mrieker/pdp8l/pics/20241210_184401.jpg

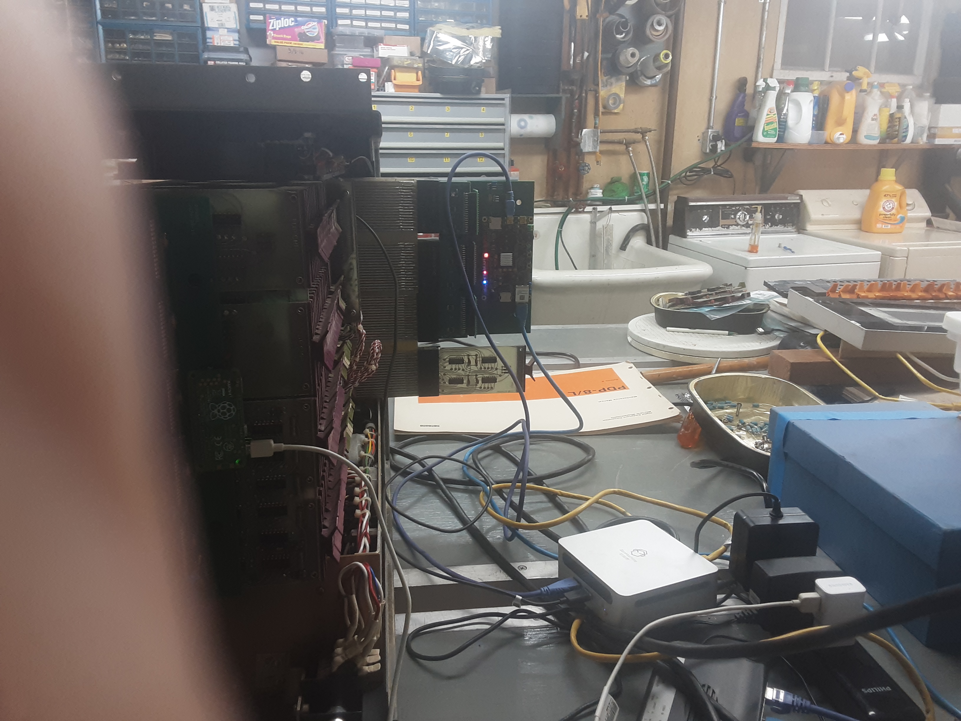
pics/20241210_184401.jpg
