mrieker/pdp8l/pics/20241210_184451.jpg

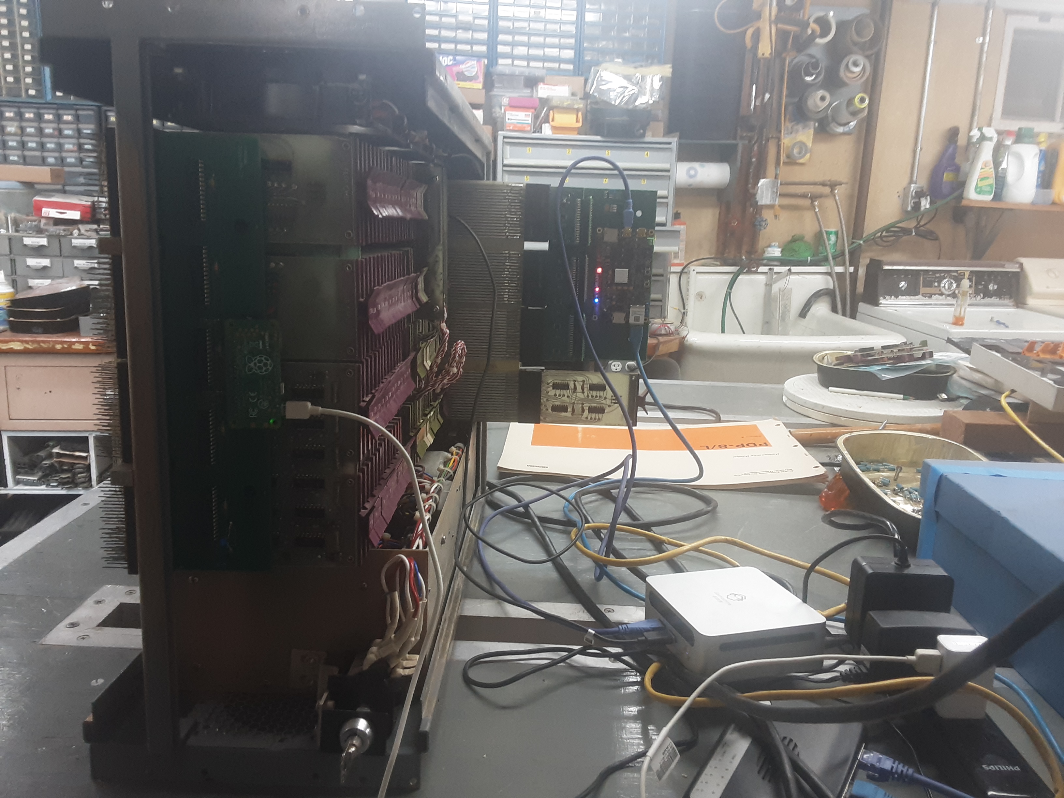
pics/20241210_184451.jpg
