mrieker/pdp8l/pics/20241210_184729.jpg

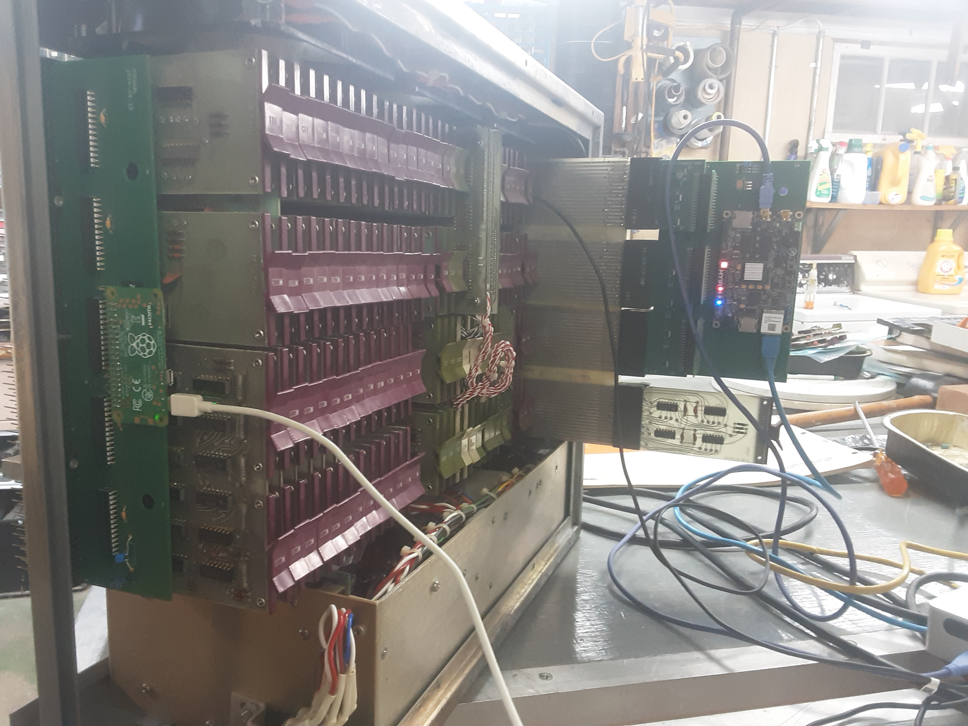
pics/20241210_184729.jpg
