mrieker/pdp8l/pics/20241225_175647.jpg

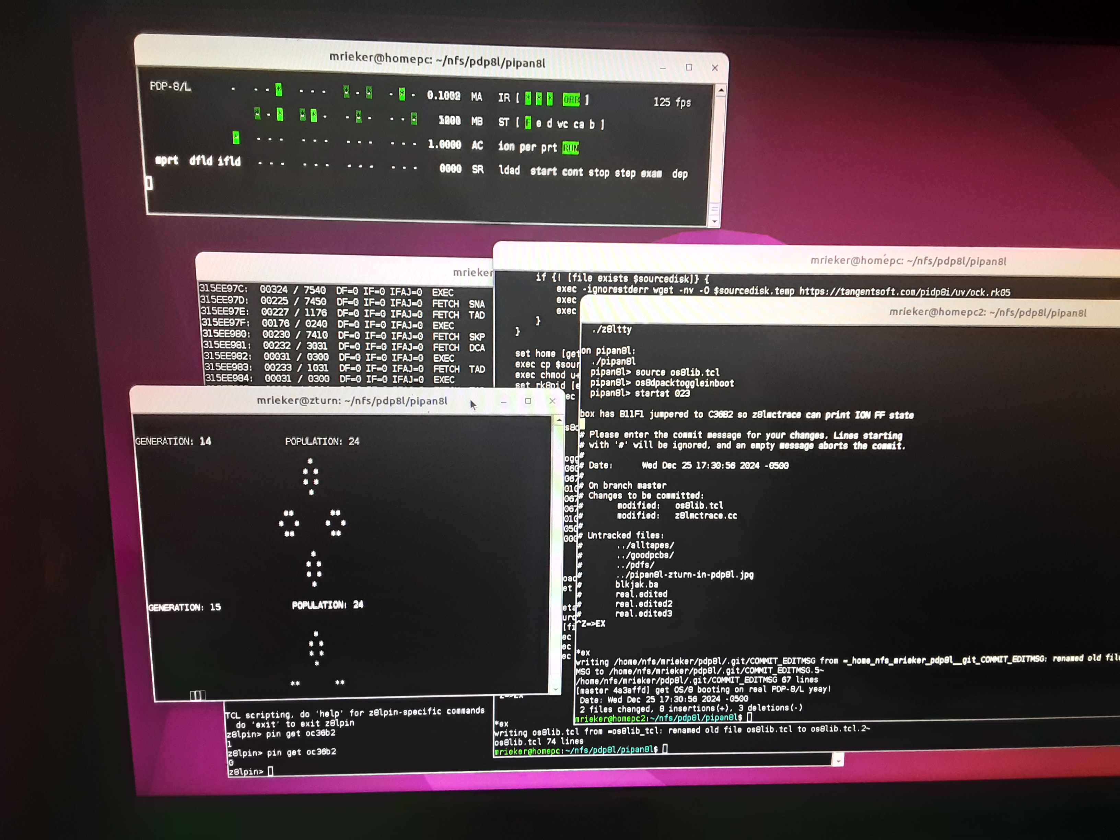
pics/20241225_175647.jpg
