mrieker/pdp8l/pics/20241225_175821.jpg

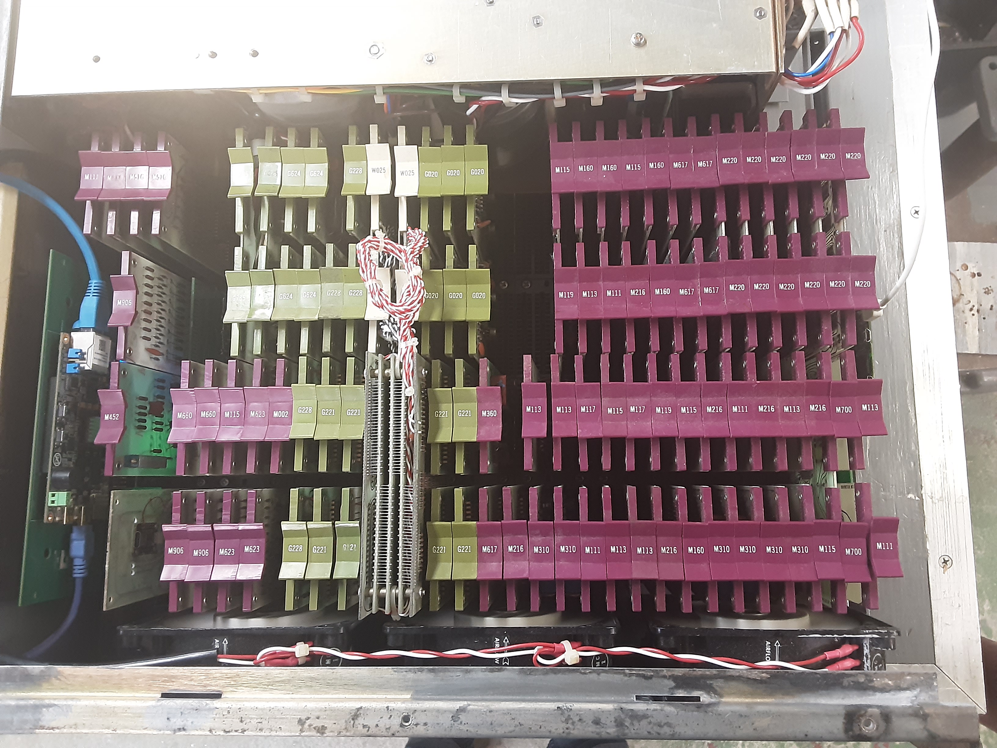
pics/20241225_175821.jpg
