mrieker/pdp8l/pics/20241225_175839.jpg

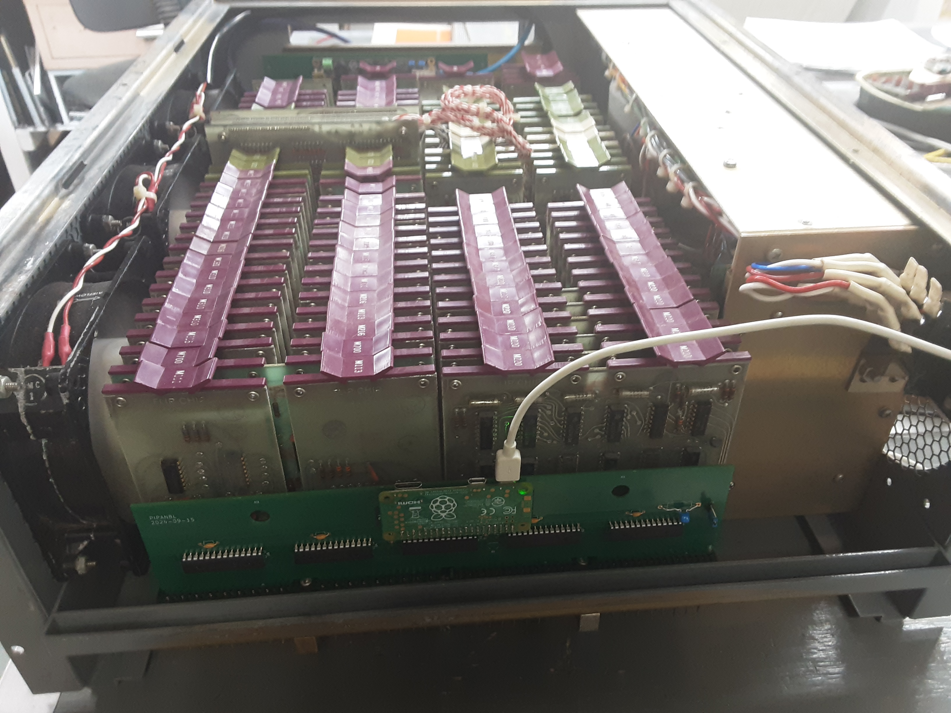
pics/20241225_175839.jpg
