mrieker/pdp8l/pics/20241225_175843.jpg

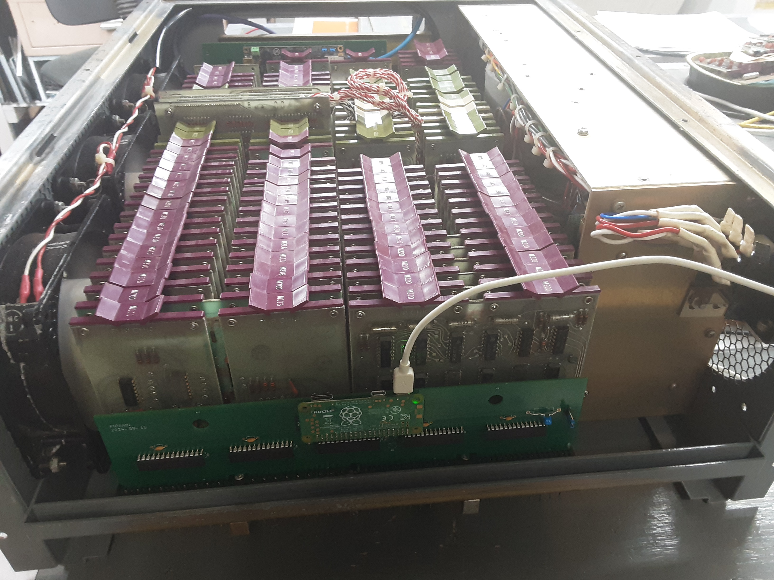
pics/20241225_175843.jpg
