mrieker/pdp8l/pics/20241225_184227.jpg

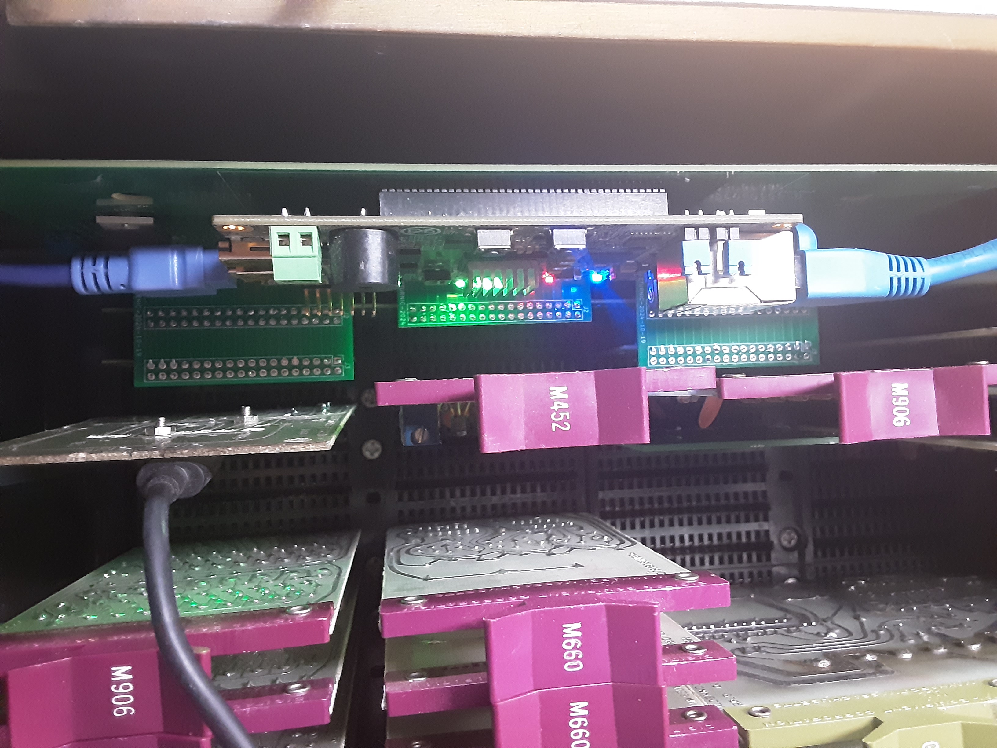
pics/20241225_184227.jpg
