mrieker/pdp8l/pics/20250225_085059.jpg

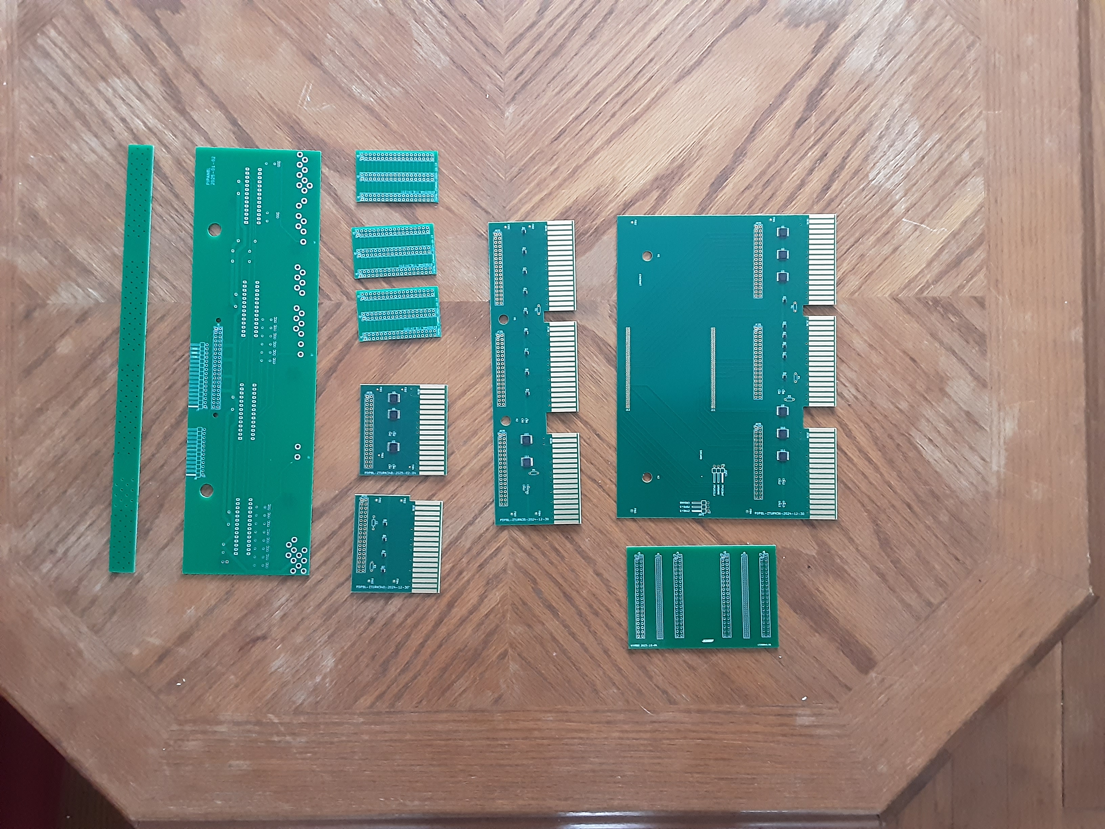
pics/20250225_085059.jpg
