mrieker/pdp8l/pics/backplane-edited.jpg

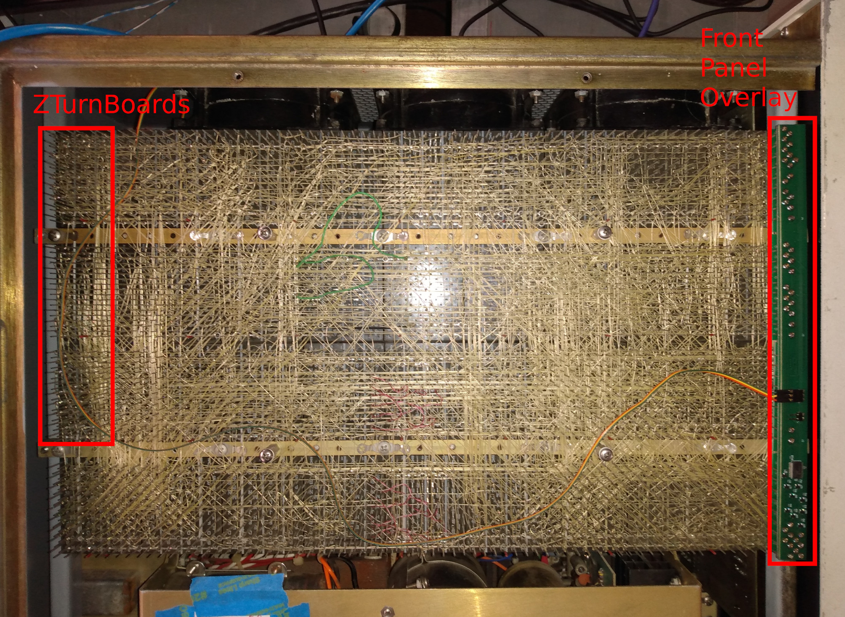
pics/backplane-edited.jpg
