mrieker/pdp8l/pipan8l/pcb3/botside.jpg

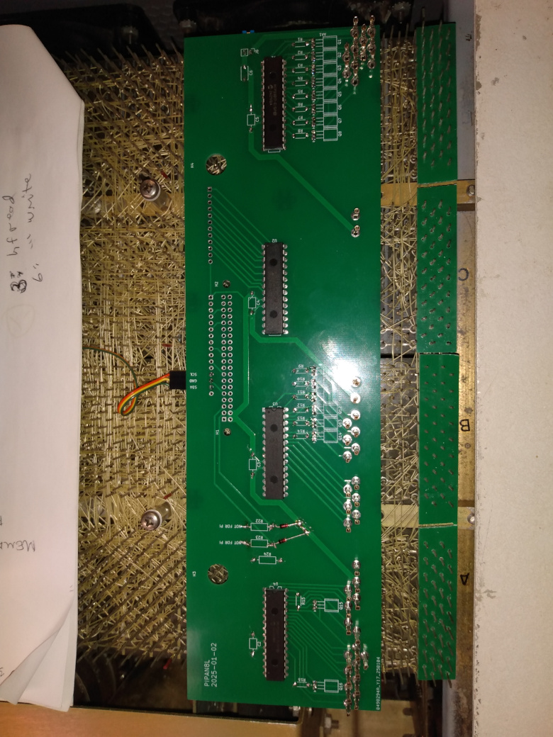
pipan8l/pcb3/botside.jpg
