mrieker/pdp8l/pipan8l/pcb3/topside.jpg

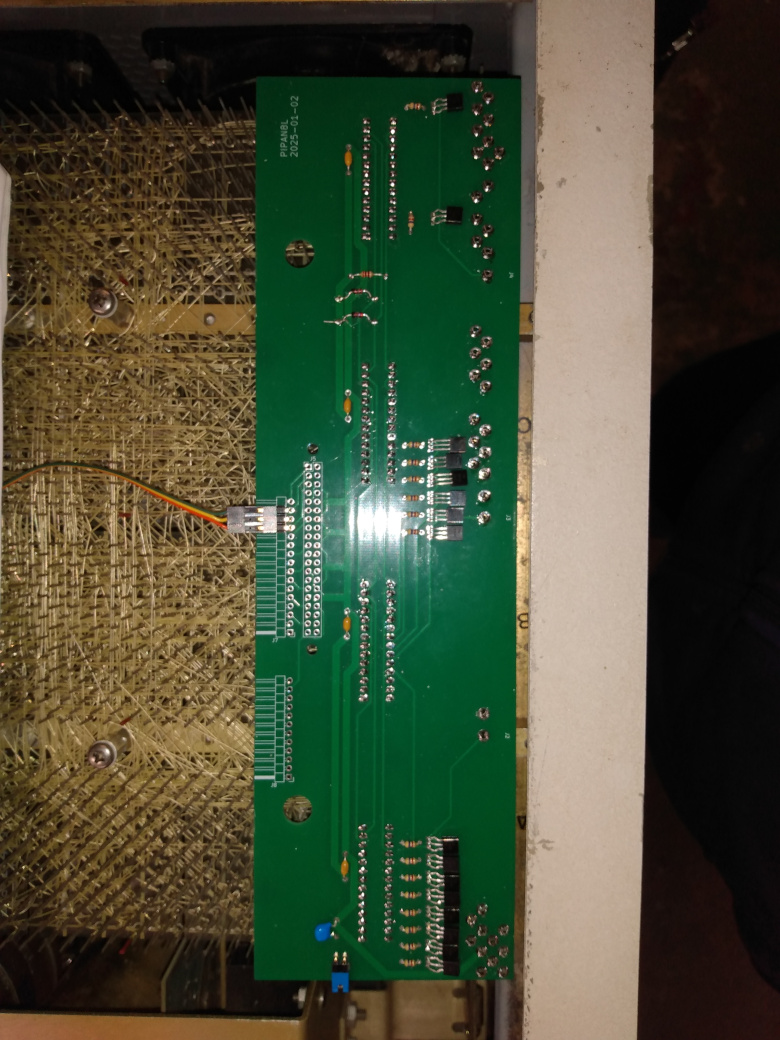
pipan8l/pcb3/topside.jpg
