mrieker/pdp8l/pipan8l/pcb4/bot-side.jpg

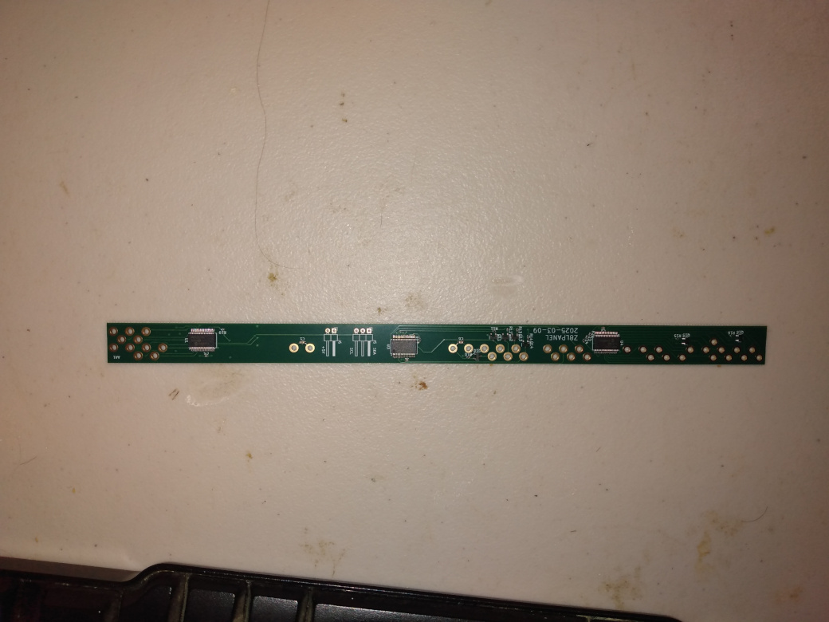
pipan8l/pcb4/bot-side.jpg
