mrieker/pdp8l/pipan8l/pcb4/plugged-in.jpg

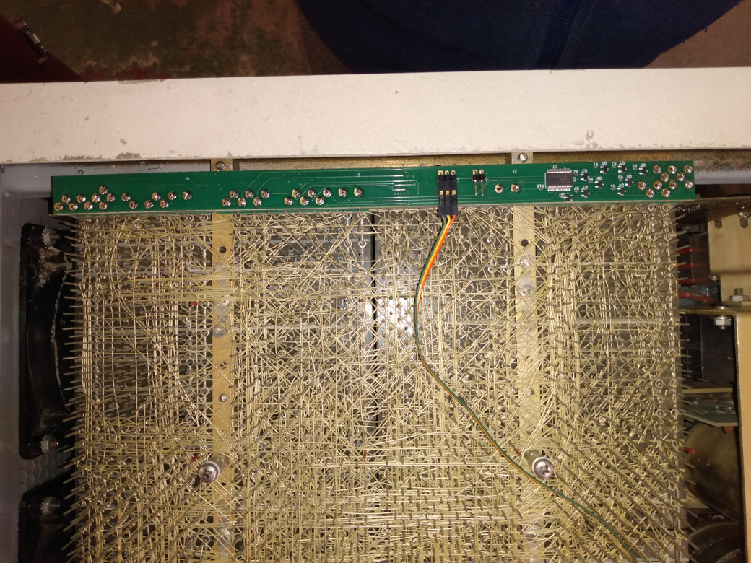
pipan8l/pcb4/plugged-in.jpg
