mrieker/pdp8l/pipan8l/pcb4/top-side.jpg

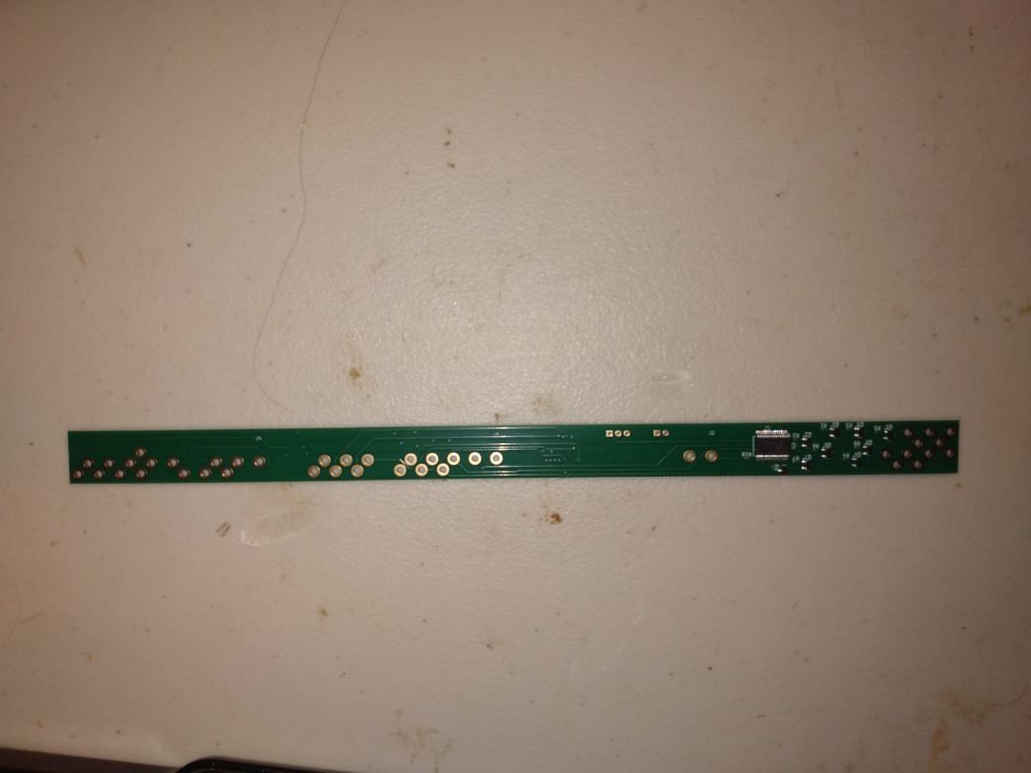
pipan8l/pcb4/top-side.jpg
