mrieker/pdp8l/ttyusbpcb/snapshot.jpg

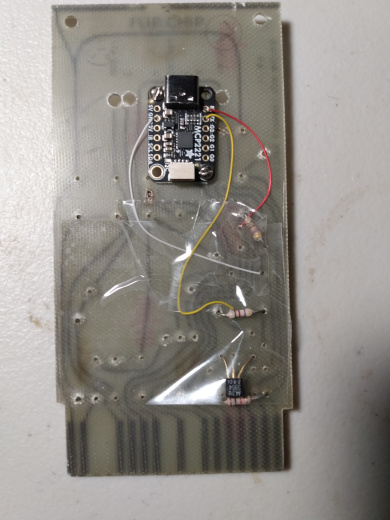
ttyusbpcb/snapshot.jpg
