mrieker/pdp8l/zturn/zturn36/zturn36snap.jpg

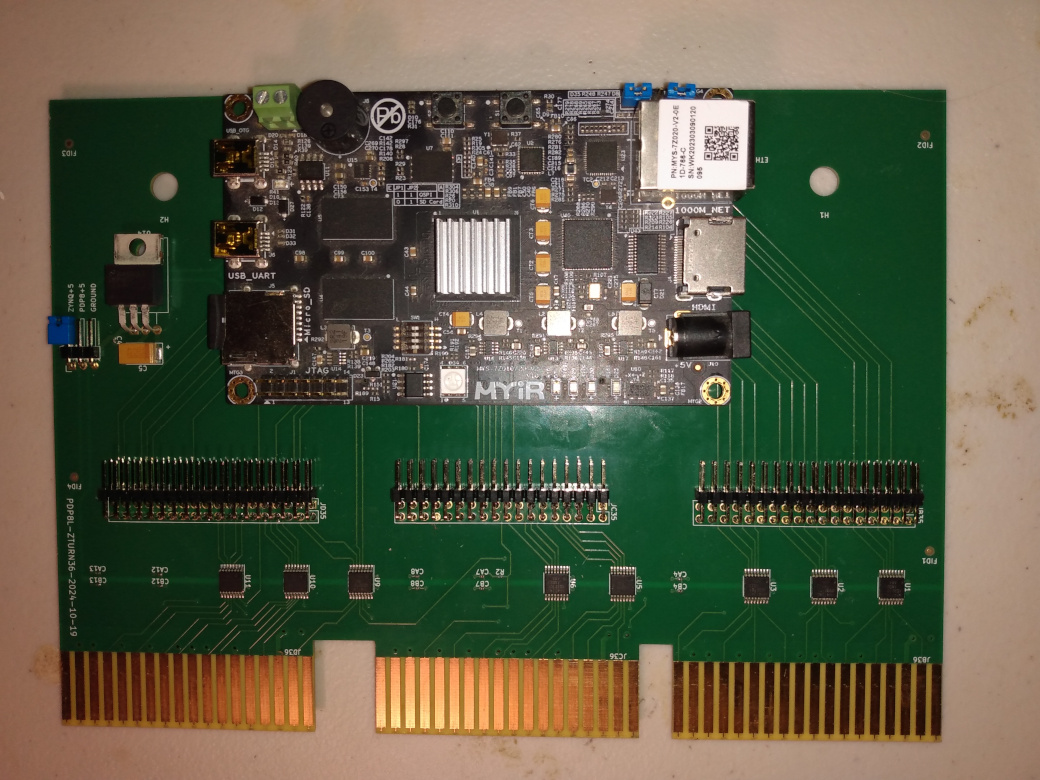
zturn/zturn36/zturn36snap.jpg
