mrieker/pdp8l/zynq/pdp8lxmem.v

//    Copyright (C) Mike Rieker, Beverly, MA USA
//    www.outerworldapps.com
//
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
//    EXPECT it to FAIL when someone's HeALTh or PROpeRTy is at RISk.
//
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
//    http://www.gnu.org/licenses/gpl-2.0.html

// PDP-8/L extended memory

// arm registers:
//  [0] = ident='XM',sizecode=1,version
//  [1] = <enable> <enlo4k> 00000000000000000000000000000 os8zap
//    enable = 0 : ignore io instructions, ie, be a dumb 4K system
//             1 : handle io instructions
//    enlo4k = 0 : PDP-8/L core stack will be used for low 4K addresses
//             1 : the low 4K of the 32K block memory will be used for low 4K addresses
//                 ...regardless of the enable bit setting
//    os8zap = 0 : nothing special
//             1 : os8 likes to do:
//                  ISZ x
//                  JMP .-1
//              ...as a delay during printing
//              zap the JMP .-1 to be:
//                  NOP ; x <= 0
//              must have enlo4k set for it to work in low 4K

//  addrlatchwid  = width to capture MA from PDP/sim
//                  TP4 of previous cycle loads MA (vol 2 p? C-7)
//  readstrobedel = delay from end of addrlatchwid to STROBE pulse
//                  time to read from RAM + make it to PDP/sim + soak thru muxes, adders, to DFF inputs
//  readstrobewid = width of STROBE pulse
//                  max 150nS or TS2 will not clear (vol 2 p? C-6)
//                  directly generates TP1 pulse
//                  TP1 delayed by 150nS is TP2 pulse
//                  TP1 delayed by 400nS is TP3 pulse
//                  TP2 loads IR during FETCH cycle
//                  TP2 loads MB during any cycle
//  writeenabdel  = delay for PDP/sim to compute writeback value in MB
//  writeenabwid  = width to write to RAM
//  writedonewid  = width of MEMDONE pulse

module pdp8lxmem (
    input CLOCK, CSTEP, RESET, BINIT,

    input armwrite,
    input[2:0] armraddr, armwaddr,
    input[31:00] armwdata,
    output[31:00] armrdata,

    input iopstart,
    input iopstop,
    input[11:00] ioopcode,
    input[11:00] cputodev,

    output reg[11:00] devtocpu,

    input freeze,

    input memstart,                 // pulse from cpu to start memory cycle (150..500nS)
    input[11:00] memaddr,
    input[11:00] memwdat,
    output reg[11:00] memrdat,
    output reg _mrdone,             // pulse to cpu saying data is available
    output reg _mwdone,             // pulse to cpu saying data has been written
    input[2:0] brkfld,              // field for dma
    output[2:0] field,              // current field being used

    input _bf_enab, _df_enab, exefet, _intack, jmpjms, ts1, ts3, tp3, _zf_enab,
    output _ea, _intinh,
    input[9:0] meminprog,
    output reg r_MA, x_MEM, hizmembus,

    input ldaddrsw,                 // load address switch
    input[2:0] ldaddfld, ldadifld,  // ifld, dfld for load address switch

    output reg[14:00] xbraddr,      // external block ram address bus
    output reg[11:00] xbrwdat,      // ... write data bus
    input[11:00] xbrrdat,           // ... read data bus
    output reg xbrenab,             // ... chip enable
    output reg xbrwena,             // ... write enable

    input  xmemblock,
    output xmemidle

    ,output reg[3:0] xmstate
    ,output reg[2:0] dfld
);

    reg ctlenab, ctllo4k, ctlwrite, intinhibeduntiljump;
    reg[2:0] lastintack;
    reg[2:0] ifld, ifldafterjump, saveddfld, savedifld;
    reg[7:0] memdelay, numcycles;
    reg[7:0] addrlatchwid, readstrobedel, readstrobewid, writeenabdel, writeenabwid, writedonewid;
    reg[9:0] exefetsr;
    reg mwhold, mwstep, mrhold, mrstep, os8zap, thisexefet;

    reg[63:00] memcycctr;

    reg[14:00] os8iszxaddr;                     // address of ISZ instruction
    reg[11:00] os8iszwdata;                     // ISZ operand value, incremented
    reg[6:0] os8iszopcad;                       // address of ISZ operand
    reg[1:0] os8step;                           // 0:looking / 1:ISZ fetch / 2:ISZ exec / 3:JMP fetch
    wire[6:0] os8jmpopcad = os8iszxaddr + 1;    // address of JMP instruction
    wire os8isourjmp = (xbraddr == { os8iszxaddr[14:07], os8jmpopcad }) &   // fetching JMP .-1 following the ISZ
                       (xbrrdat == { 5'b10101, os8iszxaddr[06:00] });

    // the _xx_enab inputs are valid in the cycle before the one they are needed in
    // ...and they go away right around the start of TS1 where they are needed
    // so we save them at the end of previous TS3 so they are valid at start of TS1 through end of TS3 that they are needed for
    reg buf_bf_enab, buf_df_enab, buf_zf_enab, lastts3;

    assign field =
                ~ buf_bf_enab ? brkfld :    // break field if cpu says so
                ~ buf_df_enab ? dfld   :    // data field if cpu says so
                ~ buf_zf_enab ? 0      :    // WC and CA cycles always use field 0
                                ifld;       // by default, use instruction field

    assign armrdata = (armraddr == 0) ? 32'h584D202E :  // [31:16] = 'XM'; [15:12] = (log2 nreg) - 1; [11:00] = version
                      (armraddr == 1) ? { ctlenab, ctllo4k, 25'b0, mrhold, mrstep, mwhold, mwstep, os8zap } :
                      (armraddr == 2) ? { _mrdone, _mwdone, field, 4'b0, dfld, ifld, ifldafterjump, saveddfld, savedifld, 4'b0, xmstate } :
                      (armraddr == 3) ? { numcycles, lastintack, buf_bf_enab, buf_df_enab, buf_zf_enab, 16'b0, os8step } :
                      (armraddr == 4) ? { writeenabdel, readstrobewid, readstrobedel, addrlatchwid } :
                      (armraddr == 5) ? { 16'b0, writedonewid, writeenabwid } :
                      (armraddr == 6) ? { memcycctr[31:00] } :
                      (armraddr == 7) ? { memcycctr[63:32] } :
                      32'hDEADBEEF;

    assign _ea = ~ (ctllo4k | (field != 0));
    assign _intinh = ~ intinhibeduntiljump;

    assign xmemidle = xmstate == 0;

    // main processing loop
    always @(posedge CLOCK) begin
        if (BINIT) begin
            if (RESET) begin
                // these get cleared on power up
                // they remain as is when start switch is pressed
                buf_bf_enab   <= 1;
                buf_df_enab   <= 1;
                buf_zf_enab   <= 1;
                ctlenab       <= 1;
                ctllo4k       <= 0;
                dfld          <= 0;
                hizmembus     <= 1;
                ifld          <= 0;
                ifldafterjump <= 0;
                lastts3       <= 0;
                mrhold        <= 0;
                mrstep        <= 0;
                mwhold        <= 0;
                mwstep        <= 0;
                os8step       <= 0;
                os8zap        <= 0;
                r_MA          <= 1;
                x_MEM         <= 1;
                xbraddr       <= 0;
                xbrwdat       <= 0;
                xbrenab       <= 0;
                xbrwena       <= 0;
                xmstate       <= 0;
                _mrdone       <= 1;
                _mwdone       <= 1;

                addrlatchwid  <=  8;                    // default extmem timing
                readstrobedel <= 35;
                readstrobewid <= 10;
                writeenabdel  <= 75;
                writeenabwid  <=  5;
                writedonewid  <= 10;
            end

            // these get cleared on power up or start switch
            intinhibeduntiljump <= 0;
            lastintack <= 0;
            numcycles  <= 0;
            saveddfld  <= 0;
            savedifld  <= 0;
            memcycctr  <= 0;
        end

        // arm processor is writing one of the registers
        // armwrite lasts only 1 fpga clock cycle
        else if (armwrite) begin
            case (armwaddr)

                // arm processor is wanting to write the registers
                1: begin
                    ctlenab  <= armwdata[31];           // save overall enabled flag
                    ctllo4k  <= armwdata[30];           // save low 4K enabled flag
                    mrhold   <= armwdata[04];
                    mrstep   <= armwdata[03];
                    mwhold   <= armwdata[02];
                    mwstep   <= armwdata[01];
                    os8zap   <= armwdata[00];           // save os8zap enabled flag
                end

                4: begin
                    addrlatchwid  <= armwdata[07:00];   // time at beg of cycle to latch address
                    readstrobedel <= armwdata[15:08];   // time after that to beg of strobe pulse
                    readstrobewid <= armwdata[23:16];   // width of strobe pulse
                    writeenabdel  <= armwdata[31:24];   // time after strobe before writing ram
                end
                5: begin
                    writeenabwid  <= armwdata[07:00];   // width of write pulse
                    writedonewid  <= armwdata[15:08];   // width of memdone pulse
                end

                6: begin
                    memcycctr[31:00] <= armwdata;
                end
                7: begin
                    memcycctr[63:32] <= armwdata;
                end
            endcase
        end else if (CSTEP) begin
            numcycles <= numcycles + 1;

            //////////////////////////////////////////////
            //  manage IF and DF and related registers  //
            //////////////////////////////////////////////

            // capture the _xx_enable signals at the end of TS3
            // they hold the values needed for the next memory cycle
            // clocking at the end of TS3 holds them valid throughout the current cycle
            // ...and gives the next cycle plenty of time to set up
            if (lastts3 & ~ ts3) begin
                buf_bf_enab <= _bf_enab;
                buf_df_enab <= _df_enab;
                buf_zf_enab <= _zf_enab;
            end
            lastts3 <= ts3;

            // maybe we have load address switch to process
            // theoretically can't happen when the processor is running
            // ...so it won't interfere with io instruction processing below
            if (ldaddrsw) begin
                dfld <= ldaddfld;
                ifld <= ldadifld;
                ifldafterjump <= ldadifld;
            end

            // maybe there is an io instruction to process
            // see mc8l memory extension, p6
            // note: if _intack is asserted, the _intack code below that saves ifld,dfld,etc has already executed at tp3 time
            //       so anything here must take that into account, using the saved values instead of current values
            else if (iopstart & (ioopcode[11:06] == 6'o62)) begin
                case (ioopcode[02:00])
                    0,1,2,3: begin

                        // check for CDFn instruction
                        if (ioopcode[00]) begin
                            // won't be followed by intack, just set the field
                            dfld <= ioopcode[05:03];
                        end

                        // check for CIFn instruction
                        // won't be followed by intack cuz it blocks interrupts
                        if (ioopcode[01]) begin
                            ifldafterjump <= ioopcode[05:03];
                            intinhibeduntiljump <= 1;
                        end
                    end
                    4: begin
                        case (ioopcode[05:03])
                            1: begin    // 6214 RDF
                                devtocpu[05:03] <= dfld;
                            end
                            2: begin    // 6224 RIF
                                devtocpu[05:03] <= ifld;
                            end
                            3: begin    // 6234 RIB
                                devtocpu[05:03] <= savedifld;
                                devtocpu[02:00] <= saveddfld;
                            end

                            4: begin    // 6244 RMF
                                dfld          <= saveddfld;
                                ifldafterjump <= savedifld;
                            end
                        endcase
                    end
                endcase
            end

            // somewhere in middle of instruction to be followed by jms 0 for an interrupt
            //  _intack = next cycle will be the exec of the jms 0 for calling interrupt service routine
            //            asserted only during TS4 (p22 C-5; p9)
            // the interrupt service routine always starts in field 0
            if (~ _intack) begin
                if (lastintack == 6) begin  // have solid 60nS of _intack in TS4 cycle
                    saveddfld <= dfld;      // save data & instruction fields
                    savedifld <= jmpjms ? ifldafterjump : ifld;
                    dfld <= 0;              // interrupt routine starts in field 0
                    ifld <= 0;
                    ifldafterjump <= 0;
                end
                if (lastintack != 7) lastintack <= lastintack + 1;
            end

            // somewhere in middle of jmp/jms, don't inhibit interrupts any more
            //  tp3    = blip near end of writing memory (our external block ram, sim's localcore array, or PDP-8/L core stack)
            //  jmpjms = JMP or JMS opcode currently in instruction register
            //  exefet = EXEC or FETCH state is next
            //
            // cases:
            //  direct JMP:
            //                      <- here with jmpjms = 0
            //   jmp fetch:  old IF
            //                      <- here with jmpjms = 1, exefet = 1
            //   next fetch: new IF
            //
            //  indirect JMP (the usual case, return-from-interrupt):
            //                      <- here with jmpjms = 0
            //   jmp fetch:  old IF
            //                      <- here with jmpjms = 1, exefet = 0
            //   jmp defer:  old IF
            //                      <- here with jmpjms = 1, exefet = 1
            //   next fetch: new IF
            //
            //  direct JMS:
            //                      <- here with jmpjms = 0
            //   jms fetch:  old IF
            //                      <- here with jmpjms = 1, exefet = 1
            //   jms exec:   new IF
            //                      <- here with jmpjms = 1, exefet = 1
            //   next fetch: new IF
            //
            //  indirect JMS:
            //                      <- here with jmpjms = 0
            //   jms fetch:  old IF
            //                      <- here with jmpjms = 1, exefet = 0
            //   jms defer:  old IF
            //                      <- here with jmpjms = 1, exefet = 1
            //   jms exec:   new IF
            //                      <- here with jmpjms = 1, exefet = 1
            //   next fetch: new IF
            //
            else if (tp3 & jmpjms & exefet) begin

                // exefet is dependent on TP3* for interrupt requests so can change during the beginning of TS4
                // then by the time the PDP clocks the major state at TP4 it is different than what we have here
                // but the MC-8/L clocks it at TP3 so we do the same here

                // since this changes things only when intinhibeduntiljump is set, exefet should be steady
                // at this point and reflect FETCH/EXEC is next assuming no interrupt pending

                // note: TP3* indicates TP3 but delayed to end of io pulses for IOT instructions, ie, beginning of TS4

                //  esetfset = eset | fset
                //  TP2,3*,4,intinhibit

                //  eset     = intok | defer & ~ jmp | fetch & ~ mb03 & ~ jmp & ~ iot & ~ opr
                //  TP2,3*,4   TP2,3*  TP4       TP2   TP4       TP2      TP2     TP2     TP2

                //  fset = ~ dset & ~ eset & ~ breakok & ~ specialcycle
                //  TP2,3*,4 TP2,3*,4 TP2,3*,4 TP4         TP4

                //  dset = fetch & mb03 & ~ iot & ~ opr
                //  TP2,4  TP4     TP2      TP2     TP2

                //  intok = intsync & intdelay & ~ intinhibit & (irmb != 600x)
                //  TP2,3*  TP3*      TP3*                       TP2

                //  breakok = ~ eset & ~ fset & ~ specialcycle & brksync
                //                                TP4            TP1

                //  specialcycle = wordcount | currentaddress
                //  TP4            TP4         TP4

                //  intstrobe = ioend | tp3 & ~ iot
                //  TP3* = start of TS4

                // MC-8/L
                //   INT_INH clock = posedge (LOAD_IF | KEY_CLEAR)  (p11 C-4)
                //   LOAD_IF       = jmpjms & tp3 & exefet  (p11 C-4)
                intinhibeduntiljump <= 0;

                // MC-8/L
                //   IF clock = posedge LOAD_IF  (p11 C-7)
                //   LOAD_IF  = jmpjms & tp3 & exefet  (p11 C-4)
                ifld <= ifldafterjump;
            end

            // processor no longer sending an IOP, stop sending data over the bus so it doesn't jam other devices
            else if (iopstop) begin
                devtocpu <= 0;
            end

            // process each intack cycle only once
            // ie, don't process another one until this one is finished
            if (_intack) lastintack <= 0;

            ////////////////////////////////////
            //  external 32KW memory control  //
            ////////////////////////////////////

            // wait for MEMSTART=1 and _EA=0 meaning PDP/sim wants to use external memory
            // follows timing from PDP-8/L maint vol 1, p 4-14
            //    0.. 250nS : latch 15-bit memory address into XBRADDR
            //  250..1600nS : read from FPGA memory, gate onto FPGAs MEMBUS for rest of cycle
            //  500.. 600nS : send STROBE pulse to PDP/sim saying read data is valid
            // 1000..1500nS : write data coming from PDP/sim MB register to FPGA memory
            // 1500..1600nS : send MEMDONE pule to PDP/sim saying write is complete

            // see if this is a FETCH or EXEC cycle
            // exefet settles sometime in the 400nS TS4 timestate (after TS3 and all the io pulses if any)
            // so sample it 100nS before the end of TS4 = 100nS before start of TS1
            if (ts1) thisexefet <= exefetsr[9];
            else exefetsr <= { exefetsr[8:0], exefet };

            // increment memory cycle counter, used for measuring memory cycle time, from one memstart to the next
            //  <62:60> = number of counters filled, 0..6 (counter freezes when >= 6)
            //  <59:48> = counter[4]
            //  <47:36> = counter[3]
            //  <35:24> = counter[2]
            //  <23:12> = counter[1]
            //  <11:00> = counter[0]
            // each counter:
            //  <11> = _EA bit
            //  <10> = didio bit
            //  <09:00> = fpga cycles - 1
            if (memcycctr[62:60] < 6) begin
                if ((xmstate == 0) & memstart) begin
                    if (memcycctr[62:60] != 5) begin
                        memcycctr[59:00] <= { memcycctr[47:00], _ea, 11'b0 };
                    end
                    memcycctr[62:60] <= memcycctr[62:60] + 1;
                end else if (memcycctr[09:00] != 1023) begin
                    memcycctr[09:00] <= memcycctr[09:00] + 1;
                end
            end

            case (xmstate)

                // wait for PDP/sim to start a memory cycle for external memory
                0: begin
                    x_MEM <= 1;

                    // if being blocked from starting (cmem wants to use extended memory),
                    // ...make sure we aren't jamming up the address bus going to the extended mem
                    if (xmemblock) begin
                        xbraddr  <= 0;
                    end

                    // not blocked, check for PDP/sim starting a memory cycle
                    else if (memstart) begin
                        hizmembus <= 1;                     // hi-Z the FPGAs MEMBUS pins so we can read PDPs MA
                        memdelay  <= addrlatchwid;          // reset memory delay line

                        // starting an internal memory cycle (internal to PDP, ie, its 4KW core stack)
                        if (_ea) xmstate <= 10;             // wait for internal memory cycle to complete

                        // starting an external memory cycle (external to PDP, ie, our 32KW memory)
                        else xmstate <= 1;                  // start processing external memory cycle
                    end

                    // if it has been a while since any MEMSTART pulse, assume the PDP is stopped
                    // clock in the PDPs MA register so it shows up on console
                    else case (meminprog)
                        7: hizmembus <= 1;                  // hi-Z the FPGAs MEMBUS pins so we can read PDPs MA
                        6: r_MA <= 0;                       // gate PDPs MA onto FPGAs MEMBUS
                                                            // zynq.v clocks it into its oMA
                        0: r_MA <= 1;                       // should be soaked in by now
                    endcase
                end

                // doing external memory cycle:
                //   give us 80nS to latch MA contents from FPGA's MEMBUS (though it really comes in around 30-40nS)
                //   this is analogous to waiting for the start of the core memory READ pulse in the real PDP
                1: begin
                    if (memdelay != 0) begin
                        memdelay <= memdelay - 1;
                        r_MA     <= 0;                      // start gating from PDP's MA bus onto FPGA MEMBUS
                    end else begin
                        memdelay <= readstrobedel;
                        r_MA     <= 1;
                        xbraddr  <= { field, memaddr };
                        xbrenab  <= 1;
                        xmstate  <= 2;
                    end
                end

                // wait another 420nS then send out STROBE pulse to PDP/sim saying data is valid
                2: begin
                    memrdat   <= ((os8step == 2) & os8isourjmp & thisexefet) ? 12'o7000 : xbrrdat;
                                            // save latest value read from extmem ram
                    x_MEM     <= 0;         // gate memrdat out to PDP via FPGAs MEMBUS
                    hizmembus <= 0;
                    if (memdelay != 0) begin
                        memdelay <= memdelay - 1;
                    end else begin
                        memdelay <= readstrobewid;
                        mrstep   <= 0;      // tell stepper we are about to stop
                        xmstate  <= 3;      // ...then start sending strobe pulse

                        // all cycles dealing with os8zap are either FETCH or EXEC
                        // so if this cycle isn't, then abandon any zap detection
                        if (~ thisexefet) os8step <= 0;
                        else case (os8step)
                            // see if have ISZ direct on page with room for a following JMP on the page
                            // if so, save address of operand and address of ISZ instruction, set to state 1
                            // if we get false positive (this isn't a FETCH), we detect that on the next cycle
                            0: begin
                                if (os8zap & (xbraddr[06:00] != 127) & (xbrrdat[11:07] == 5'b01001)) begin
                                    os8iszopcad <= xbrrdat[06:00];
                                    os8iszxaddr <= xbraddr;
                                    os8step <= 1;
                                end
                            end
                            // if prev cycle looked like an ISZ direct on page, see if this cycle is accessing operand
                            // if so, save operand and set to state 2
                            // if this cycle is a FETCH and not and EXEC, we detect this when we get a writeback of
                            // ...the operand below because it won't be incremented
                            // so we will know that this is an EXEC and the previous cycle was a FETCH of an ISZ
                            1: begin
                                if (xbraddr == { os8iszxaddr[14:07], os8iszopcad }) begin
                                    os8iszwdata <= xbrrdat + 1;
                                    os8step <= 2;
                                end else begin
                                    os8step <= 0;
                                end
                            end
                            // if prev cycle accessed ISZ operand and this is a JMP .-1,
                            //   return a NOP opcode instead of JMP .-1 (see above memrdat <= ...)
                            //   also change mem addr to re-write ISZ operand = 0 during write portion of cycle
                            2: begin
                                if (os8isourjmp) begin
                                    os8step <= 3;
                                    xbraddr <= { os8iszxaddr[14:07], os8iszopcad };
                                end else begin
                                    os8step <= 0;
                                end
                            end
                            // zap complete
                            3: os8step <= 0;
                        endcase
                    end
                end

                // end the STROBE pulse after 100nS
                // then we're 600nS into the cycle
                3: begin
                    if (~ mrhold | mrstep) begin
                        if (memdelay != 0) begin
                            memdelay <= memdelay - 1;
                            _mrdone  <= 0;
                        end else begin
                            memdelay <= writeenabdel;
                            _mrdone  <= 1;
                            xmstate  <= 4;
                        end
                    end
                end

                // write to FPGA memory after another 850nS
                // then we're 1450nS into the cycle
                // supposedly the PDP has come up with data by then
                4: begin
                    if (memdelay != 0) begin
                        memdelay <= memdelay - 1;
                    end else begin
                        memdelay <= writeenabwid;
                        xbrwdat  <= (os8step == 3) ? 12'o0000 : memwdat;
                        xbrwena  <= 1;
                        xmstate  <= 5;

                        // abandon os8zap if we are expecting this cycle to be the incremented ISZ operand
                        if ((os8step == 2) & (memwdat != os8iszwdata)) os8step <= 0;
                    end
                end

                // write the FPGA memory for 50nS
                // then we're 1500nS into the cycle
                5: begin
                    if (memdelay != 0) begin
                        memdelay <= memdelay - 1;
                    end else if (~ armwrite) begin
                        memdelay <= writedonewid;
                        mwstep   <= 0;              // tell stepper (eg z8lmctrace.cc) cycle is complete
                        xbrenab  <= 0;              // stop writing to FPGA 32KW memory
                        xbrwena  <= 0;
                        xbrwdat  <= 0;
                        xmstate  <= 6;
                    end
                end

                // output 100nS write complete pulse to processor
                // then we're 1600nS into the cycle
                // but wait for stepper if we are doing stepping
                // and wait if frozen by shadow error
                6: begin
                    if (~ freeze & (~ mwhold | mwstep)) begin
                        if (memdelay != 0) begin
                            _mwdone  <= 0;
                            memdelay <= memdelay - 1;
                        end else begin
                            _mwdone  <= 1;
                            xmstate  <= 0;
                            if (xmemblock) begin
                                xbraddr <= 0;
                            end
                        end
                    end
                end

                // start of memory cycle using core memory
                // grab a copy of the MA so it shows up on console
                // FPGA MEMBUS pins are already in hi-Z
                10: begin
                    if (memdelay != 0) begin
                        memdelay <= memdelay - 1;
                        r_MA     <= 0;  // start gating from PDP's MA bus onto FPGA MEMBUS for 80nS
                    end else begin
                        r_MA     <= 1;  // 80nS is up, stop gating MA onto FGPA MEMBUS
                        xmstate  <= 11;
                    end
                end

                // send out zeroes to FPGA MEMBUS to open-drain the transistors
                // so they don't interfere with PDP reading its own core memory
                11: begin
                    hizmembus <= 0;
                    if (~ memstart) begin
                        xmstate <= 0;
                    end
                end
            endcase
        end
    end
endmodule
