mrieker/pdp8l/zynq/pdp8lsim.v

//    Copyright (C) Mike Rieker, Beverly, MA USA
//    www.outerworldapps.com
//
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
//    EXPECT it to FAIL when someone's HeALTh or PROpeRTy is at RISk.
//
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
//    http://www.gnu.org/licenses/gpl-2.0.html

// PDP-8/L-like processor, using the signals on the B,C,D 34,35,36 connectors plus front panel

module pdp8lsim (
    input CLOCK, CSTEP, RESET,  // fpga 100MHz clock and reset
    input iBEMA,                // B35-T2,p5 B-7,J11-45,,B25,asserted when address > 07777
    input i_CA_INCRMNT,         // C35-M2,p15 A-3,J11-30,,C25,?? NOT ignored in PDP-8/L see p2 D-2
    input i_DATA_IN,            // C36-M2,p15 B-2,J11-32,,,
    input[11:00] iINPUTBUS,     // D34-B1,p15 B-8,PIOBUSA,,,gated out to CPU by x_INPUTBUS
    input iMEMINCR,             // C36-T2,p15 B-1,J11-18,,,
    input[11:00] i_MEM,         // B35-D1,p19 C-7,MEMBUSH,,,gated out to CPU by x_MEM
    input i_MEM_P,              // B35-B1,p19 C-8,MEMBUSA,,,gated out to CPU by x_MEM
    input i3CYCLE,              // C35-K2,p15 A-3,J11-38,,C22,
    input iAC_CLEAR,            // D34-P2,p15 C-2,J12-27,,D33,gated out to CPU by x_INPUTBUS
    input iBRK_RQST,            // C36-K2,p15 B-3,J11-36,,,"used on p5 B-2, clocked by TP1"
    input[11:00] iDMAADDR,      // C36-B1,p15 B-8,DMABUSB,,,gated out to CPU by x_DMAADDR
    input[11:00] iDMADATA,      // C35-B1,p15 A-8,DMABUSA,,,gated out to CPU by x_DMADATA
    input i_EA,                 // B34-B1,p18 C-8,J11-53,,B30,high: use CPU core stack for mem cycle; low: block using CPU core stack
    input iEMA,                 // B35-V2,p5 B-7,J11-51,,B29,goes to EA light bulb on front panel
    input iINT_INHIBIT,         // B36-L1,p9 B-3,J12-66,,,
    input iINT_RQST,            // D34-M2,p15 C-3,J12-23,,D32,open collector out to CPU
    input iIO_SKIP,             // D34-K2,p15 C-3,J12-28,,D30,gated out to CPU by x_INPUTBUS
    input i_MEMDONE,            // B34-V2,p4 C-7,J11-55,,B32,gated out to CPU by x_MEM
    input i_STROBE,             // B34-S2,p4 C-6,J11-59,,B35,gated out to CPU by x_MEM
    output[11:00] oBAC,         // D36-B1,p15 D-8,PIOBUSA,,,gated onto PIOBUS by r_BAC
    output oBIOP1,              // D36-K2,p15 D-3,J12-34,,,
    output oBIOP2,              // D36-M2,p15 D-3,J12-32,,,
    output oBIOP4,              // D36-P2,p15 D-2,J12-26,,,
    output[11:00] oBMB,         // D35-B1,p15 D-8,PIOBUSH,,,gated from CPU onto PIOBUS by r_BMB
    output oBTP2,               // B34-T2,p4 C-5,J11-61,,B36,
    output oBTP3,               // B36-H1,p4 C-4,J12-73,,,
    output oBTS_1,              // D36-T2,p15 D-1,J12-25,,,
    output oBTS_3,              // D36-S2,p15 D-2,J12-22,,,
    output reg o_BWC_OVERFLOW,  // C35-P2,p15 A-2,J11-16,,C33,
    output o_B_BREAK,           // C36-P2,p15 B-2,J11-26,,,
    output oE_SET_F_SET,        // B36-D2,p22 C-3,J12-72,,,
    output oJMP_JMS,            // B36-E2,p22 C-3,J11-63,,,
    output oLINE_LOW,           // B36-V2,p18 B-7,J12-43,,,?? op amp output maybe needs clipping diodes
    output[11:00] oMA,          // B34-D1,p22 D-8,MEMBUSH,,,gated from CPU onto MEMBUS by r_MA
    output oMEMSTART,           // B34-P2,p4 D-8,J11-57,,B33,
    output reg o_ADDR_ACCEPT,   // C36-S2,p15 S-2,J11-22,,,
    output o_BF_ENABLE,         // B36-E1,p22 C-6,J12-69,,,
    output oBUSINIT,            // C36-V2,p15 B-1,J11-9,,,active high bus init
    output oB_RUN,              // D34-S2,p15 C-1,J12-29,,D36,run flipflop on p4 B-2
    output o_DF_ENABLE,         // B36-B1,p22 C-7,J12-65,,,
    output o_KEY_CLEAR,         // B36-J1,p22 C-5,J12-68,,,
    output o_KEY_DF,            // B36-S1,p22 C-4,J12-44,,,
    output o_KEY_IF,            // B36-P1,p22 C-4,J12-46,,,
    output o_KEY_LOAD,          // B36-H2,p22 C-3,J11-85,,,
    output o_LOAD_SF,           // B36-M1,p22 C-5,J12-52,,,
    output o_SP_CYC_NEXT,       // B36-D1,p22 C-6,J12-67,,,

    // front panel
    output[11:00] lbAC,
    output lbBRK,
    output lbCA,
    output lbDEF,
    output lbEA,
    output lbEXE,
    output lbFET,
    output lbION,
    output[2:0] lbIR,
    output lbLINK,
    output[11:00] lbMA,
    output[11:00] lbMB,
    output reg lbPRTE,
    output lbRUN,
    output lbWC,
    input swCONT,
    input swDEP,
    input swDFLD,
    input swEXAM,
    input swIFLD,
    input swLDAD,
    input swMPRT,
    input swSTEP,     // KEYSS+IREF (p4 B-6)  clears the RUN FF at any TP3 (p4 B-2)
    input swSTOP,
    input[11:00] swSR,
    input swSTART

    // debug
    ,output reg[3:0] majstate
    ,output reg[3:0] nextmajst
    ,output reg[5:0] timedelay
    ,output reg[4:0] timestate
    ,output reg[9:0] cyclectr
    ,output reg lastswLDAD
    ,output reg lastswSTART
    ,output debounced
    ,output memen
);

    localparam MS_HALT  =  0;       // waiting for console
    localparam MS_FETCH =  1;       // memory cycle is fetching instruction
    localparam MS_DEFER =  2;       // memory cycle is reading pointer
    localparam MS_EXEC  =  3;       // memory cycle is for executing instruction
    localparam MS_WC    =  4;       // memory cycle is for incrementing dma word count
    localparam MS_CA    =  5;       // memory cycle is for reading dma address
    localparam MS_BRK   =  6;       // memory cycle is for dma data word transfer
    localparam MS_INTAK =  7;       // memory cycle is for interrupt acknowledge
    localparam MS_DEPOS =  8;       // memory cycle is for deposit switch
    localparam MS_EXAM  =  9;       // memory cycle is for examine switch

    localparam TS_TSIDLE  =  0;     // figure out what to do next, does console switch processing if not running
    localparam TS_TS1BODY =  1;     // tell memory to start reading location addressed by MA
    localparam TS_TP1BEG  =  2;
    localparam TS_TP1END  =  3;
    localparam TS_TS2BODY =  4;     // get contents of memory into MB and modify according to majstate S_...
    localparam TS_TP2BEG  =  5;
    localparam TS_TP2END  =  6;
    localparam TS_TS3BODY =  7;     // write contents of MB back to memory
    localparam TS_TP3BEG  =  8;
    localparam TS_TP3END  =  9;
    localparam TS_BEGIOP1 = 10;
    localparam TS_DOIOP1  = 11;     // maybe output IOP1
    localparam TS_BEGIOP2 = 12;
    localparam TS_DOIOP2  = 13;     // maybe output IOP2
    localparam TS_BEGIOP4 = 14;
    localparam TS_DOIOP4  = 15;     // maybe output IOP4
    localparam TS_TS4BODY = 16;     // finish up instruction (modify ac, link, pc, etc)
    localparam TS_TP4BEG  = 17;
    localparam TS_TP4END  = 18;

    // general processor state
    reg hidestep, intdelayed, intenabled, ldad;
    reg lastswCONT, lastswDEP, lastswEXAM;
    reg irusedf, link, memen, memidle;
    wire runff, tp1, tp2, tp3, tp4, ts1, ts2, ts3, ts4;
    reg[2:0] ireg;
    reg[3:0] hltbrkintfet;
    reg[11:00] acum, madr, mbuf, newma, pctr;
    reg[23:00] debounce;

    // various outputs that can be derived with a few gates or passthrough
    assign runff       = majstate != MS_HALT;
    assign oBAC        = acum;
    assign oBIOP1      = (timestate == TS_DOIOP1) & mbuf[00];
    assign oBIOP2      = (timestate == TS_DOIOP2) & mbuf[01];
    assign oBIOP4      = (timestate == TS_DOIOP4) & mbuf[02];
    assign oBMB        = mbuf;
    assign oBTP2       = tp2;
    assign oBTP3       = tp3;
    assign oBTS_1      = ts1;
    assign oBTS_3      = ts3;
    assign oBUSINIT    = RESET | (~ runff & swSTART);   // power-on reset or start switch and mftp0 (p4 A-3)
    assign oJMP_JMS    = (ireg[2:1] == 2);              // JMP or JMS is loaded in IR (p22 C-2, p5 C-6)
    assign oLINE_LOW   = RESET;
    assign oMA         = madr;
    assign oMEMSTART   = (timestate == TS_TS1BODY);
    assign oB_RUN      = runff;
    assign o_KEY_DF    = ~ swDFLD;
    assign o_KEY_IF    = ~ swIFLD;
    assign o_KEY_LOAD  = ~ ldad;                        // load address switch cycle (p22 C-2, not exact match)
    assign o_KEY_CLEAR = 1;                             // B36-J1,p22 C-5,J12-68,,,

    assign lbAC   = acum;
    assign lbBRK  = (majstate == MS_BRK);
    assign lbCA   = (majstate == MS_CA);
    assign lbDEF  = (majstate == MS_DEFER);
    assign lbEA   = ~ i_EA;
    assign lbEXE  = (majstate == MS_EXEC) | (majstate == MS_INTAK);
    assign lbFET  = (majstate == MS_FETCH);
    assign lbION  = intenabled;
    assign lbIR   = ireg;
    assign lbLINK = link;
    assign lbMA   = madr;
    assign lbMB   = mbuf;
    assign lbRUN  = runff;
    assign lbWC   = (majstate == MS_WC);

    assign debounced = debounce[1]; // 84mS:[23];

    // currently in BREAK state
    assign o_B_BREAK = majstate != MS_BRK;

    // these signals are valid from beginning of TS3 to beginning of next TS3
    // before TS3, they describe the current state
    // but at one clock cycle into TS3, they describe the next state
    assign oE_SET_F_SET  = (nextmajst == MS_EXEC) | (nextmajst == MS_INTAK) | (nextmajst == MS_FETCH);  // mem cycles is EXEC or FETCH
    assign o_DF_ENABLE   = ~ ((nextmajst == MS_EXEC) & irusedf);                // next mem cycle uses DF (p22 C-7)
    assign o_SP_CYC_NEXT = ~ ((nextmajst == MS_WC) | (nextmajst == MS_CA));     // next mem cycle is MS_WC or MS_CA, use field 0 (p22 C-6, p5 C-3, also p5 B-2)
    assign o_BF_ENABLE   = ~  (nextmajst == MS_BRK);                            // next mem cycle is MS_BRK[WH], use break field (dma extended address bits) for next mem access (p5 D-2)
    assign o_LOAD_SF     = ~ ((nextmajst == MS_INTAK) & ts4);                   // next mem cycle is exec of JMS 0 used for interrupt cycle
                                                                                // ...gated with TS4 like real PDP (p22 C-5; p9)

    // local memory (presumably inferred block memory)
    reg[11:00] localcore[4095:0000];

    // calculate effective address for memory reference instructions
    // valid in fetch cycle after ts2
    wire[11:00] effaddr = { (mbuf[07] ? madr[11:07] : 5'b0), mbuf[06:00] };

    // address being accessed this cycle is protected with mem prot switch
    wire prtad = swMPRT & ~ iBEMA & (madr[11:07] == 5'o37);

    // calculate accumulator and link for tad instruction
    wire[11:00] tadacum;
    wire tadlink;
    assign { tadlink, tadacum } = { link, acum } + { 1'b0, mbuf };

    // calculate accumulator and link for group 1 instruction
    reg[11:00] g1acum, g1acumraw;
    reg g1link, g1linkraw;

    always @(*) begin
        // handle cla, cll, cma, cll, iac bits
        { g1linkraw, g1acumraw } = { (mbuf[06] ? 1'b0 : link) ^ mbuf[04], (mbuf[07] ? 12'b0 : acum) ^ (mbuf[05] ? 12'o7777 : 12'o0000) } + { 12'b0, mbuf[00] };
        // handle rotate bits
        case (mbuf[03:01])
            2: { g1link, g1acum } = { g1acumraw, g1linkraw };                           // rol 1
            3: { g1link, g1acum } = { g1acumraw[10:00], g1linkraw, g1acumraw[11] };     // rol 2
            4: { g1link, g1acum } = { g1acumraw[00], g1linkraw, g1acumraw[11:01] };     // ror 1
            5: { g1link, g1acum } = { g1acumraw[01:00], g1linkraw, g1acumraw[11:02] };  // ror 2
            default: { g1link, g1acum } = { g1linkraw, g1acumraw };                     // all else, nop
        endcase
    end

    // calculate skip condition for group 2 instruction
    wire g2skip = ((mbuf[06] & acum[11]) |    // SMA
                   (mbuf[05] & (acum == 0)) | // SZA
                   (mbuf[04] & link)) ^       // SNL
                    mbuf[03];                 // reverse

    // calculate accumulator for group 2 instruction
    wire[11:00] g2acum = (mbuf[07] ? 0 : acum) | (mbuf[02] ? swSR : 0);

    // this memory cycle does io
    wire withio = (majstate == MS_FETCH) & (ireg == 6);

    // get incoming ac bits from io bus
    wire[11:00] ioac = (iAC_CLEAR ? 0 : acum) | iINPUTBUS;

    // data written back to memory during break cycle
    wire[11:00] breakdata = (i_DATA_IN ? mbuf : iDMADATA) + { 11'b0, iMEMINCR };

    // major state following last cycle of current instruction
    always @(*) begin

        // maybe console says to halt
        if (swSTOP | swSTEP) hltbrkintfet <= MS_HALT;

        // maybe opcode says to halt
        else if ((majstate == MS_FETCH) & ((mbuf & 12'o7403) == 12'o7402)) hltbrkintfet <= MS_HALT;

        // if there is a dma request pending, start doing the dma
        else if (iBRK_RQST) hltbrkintfet <= i3CYCLE ? MS_WC : MS_BRK;

        // if interrupt requested, interrupts are enabled via 6001 (ION),
        // and they aren't inhibited via 62x2/62x3 (CIF), next is int ack
        else if (iINT_RQST &                                            // some device is requesting an interrupt
                    intenabled &                                        // 6001 was executed at least one instruction ago
                    ~ ((ireg == 6) & (mbuf[08:00] == 9'o002)) &         // not blocked by current 6002 (IOF) instruction
                    (~ iINT_INHIBIT | oJMP_JMS) &                       // not blocked by prior 62x2/62x3 until jump or currently jumping
                    ~ ((ireg == 6) & ((mbuf[08:00] & 9'o706) == 9'o202))) begin // not blocked by 62x2/62x3 currently executing
            hltbrkintfet <= MS_INTAK;
        end

        // otherwise we fetch
        else hltbrkintfet <= MS_FETCH;
    end

    // main processing loop
    // set tp1 near end of ts1, then this circuit will transition to ts2 then clear tp1
    // likewise for ts2, 3, 4, but do not enter ts4 if 'withio' is set

    assign tp1 = (timestate == TS_TP1BEG) | (timestate == TS_TP1END);
    assign tp2 = (timestate == TS_TP2BEG) | (timestate == TS_TP2END);
    assign tp3 = (timestate == TS_TP3BEG) | (timestate == TS_TP3END);
    assign tp4 = (timestate == TS_TP4BEG) | (timestate == TS_TP4END);

    assign ts1 =                            (timestate == TS_TS1BODY) | (timestate == TS_TP1BEG);
    assign ts2 = (timestate == TS_TP1END) | (timestate == TS_TS2BODY) | (timestate == TS_TP2BEG);
    assign ts3 = (timestate == TS_TP2END) | (timestate == TS_TS3BODY) | (timestate == TS_TP3BEG);
    assign ts4 = ((timestate == TS_TP3END) & ~ withio) | (timestate == TS_TS4BODY) | (timestate == TS_TP4BEG);

    always @(posedge CLOCK) begin

        if (RESET) begin
            timedelay <= 0;
            timestate <= TS_TSIDLE;

            debounce    <= 0;
            hidestep    <= 0;
            intdelayed  <= 0;
            intenabled  <= 0;
            ldad        <= 0;
            lastswCONT  <= 0;
            lastswDEP   <= 0;
            lastswEXAM  <= 0;
            lastswLDAD  <= 0;
            lastswSTART <= 0;
            lbPRTE      <= 0;
            majstate    <= MS_HALT;
            memen       <= 0;
            memidle     <= 0;
            nextmajst   <= MS_HALT;

            o_BWC_OVERFLOW <= 1;
            o_ADDR_ACCEPT  <= 1;

            cyclectr      <= 0;
        end else if (CSTEP) begin
            cyclectr      <= cyclectr + 1;

            case (timestate)

                TS_TSIDLE: begin
                    timedelay <= 0;

                    case (majstate)

                        // not running, process console switches
                        MS_HALT: begin

                            // load address switch
                            if (debounced & lastswLDAD & ~ swLDAD) begin
                                ldad      <= 1;
                                madr      <= swSR;
                                pctr      <= swSR;
                                majstate  <= MS_EXAM;
                                nextmajst <= MS_EXAM;
                            end

                            // examine switch
                            else if (debounced & lastswEXAM & ~ swEXAM) begin
                                madr      <= pctr;
                                pctr      <= pctr + 1;
                                majstate  <= MS_EXAM;
                                nextmajst <= MS_EXAM;
                            end

                            // deposit switch
                            else if (debounced & lastswDEP & ~ swDEP) begin
                                madr      <= pctr;
                                pctr      <= pctr + 1;
                                majstate  <= MS_DEPOS;
                                nextmajst <= MS_DEPOS;
                            end

                            // continue switch
                            else if (debounced & lastswCONT & ~ swCONT) begin
                                madr      <= pctr;
                                majstate  <= MS_FETCH;
                                nextmajst <= MS_FETCH;
                                timestate <= TS_TS1BODY;
                            end

                            // start switch
                            else if (debounced & lastswSTART & ~ swSTART) begin
                                acum       <= 0;
                                hidestep   <= 0;
                                intdelayed <= 0;
                                intenabled <= 0;
                                link       <= 0;
                                madr       <= pctr;
                                majstate   <= MS_FETCH;
                                nextmajst  <= MS_FETCH;
                                timestate  <= TS_TS1BODY;
                            end
                        end

                        // all others just start the memory cycle
                        default: timestate <= TS_TS1BODY;
                    endcase
                end

                ////////////////////////////////////////////////
                //  read memory from address i_EA,MA into MB  //
                ////////////////////////////////////////////////

                // memory is being read at address in MA, either internal or external memory
                // MEMSTART is asserted during this interval
                // clock read data from internal or external memory into MB at the end
                TS_TS1BODY: begin
                    if (timedelay == 0) begin
                        lbPRTE    <= 0;
                        ldad      <= 0;
                        memen     <= i_EA;
                        timedelay <= 1;
                    end else if (memen) begin
                        if (timedelay != 50) timedelay <= timedelay + 1;
                        else begin
                            mbuf      <= localcore[madr];
                            timedelay <= 0;
                            timestate <= TS_TP1BEG;
                        end
                    end else begin
                        if (! i_STROBE) begin
                            mbuf      <= ~ i_MEM;
                            timedelay <= 0;
                            timestate <= TS_TP1BEG;
                        end
                    end
                end

                TS_TP1BEG: begin
                    if (timedelay != 2) timedelay <= timedelay + 1;
                    else timestate <= TS_TP1END;
                end

                TS_TP1END: begin
                    o_ADDR_ACCEPT <= 1;
                    if (timedelay != 5) begin
                        timedelay <= timedelay + 1;
                    end else if (memen | i_STROBE) begin
                        timedelay <= 0;
                        timestate <= TS_TS2BODY;
                    end
                end

                //////////////////////////////////////////
                //  modify MB according to major state  //
                //////////////////////////////////////////

                // allow 210nS for the data in MB to be modified by the instruction if appropriate
                TS_TS2BODY: begin
                    if (timedelay != 21) timedelay <= timedelay + 1;
                    else begin
                        case (majstate)
                            MS_FETCH: begin
                                intenabled <= intdelayed;
                                ireg       <= mbuf[11:09];
                                irusedf    <= ~ mbuf[11] & mbuf[08];
                                pctr       <= pctr + 1;
                            end
                            MS_DEFER: if (madr[11:03] == 1) mbuf <= mbuf + 1;
                            MS_EXEC, MS_INTAK: case (ireg)
                                2: begin if (prtad) lbPRTE <= 1; else mbuf <= mbuf + 1; end    // isz
                                3: begin if (prtad) lbPRTE <= 1; else mbuf <= acum; end        // dca
                                4: begin if (prtad) lbPRTE <= 1; else mbuf <= pctr; end        // jms
                            endcase
                            MS_WC: begin
                                if (prtad) lbPRTE <= 1; else mbuf <= mbuf + 1;
                                // middle of wc with count just read, detect count overflow
                                // PDP-8/L clocks it with TP2 (vol 2, p5 D-5)
                                o_BWC_OVERFLOW <= (mbuf != 12'o7777);
                            end
                            MS_CA: if (~ i_CA_INCRMNT) begin
                                if (prtad) lbPRTE <= 1; else mbuf <= mbuf + 1;
                            end
                            MS_BRK: if (~ i_DATA_IN | iMEMINCR) begin
                                // data must be ready in time for TS3 (pdp-8/l user's handbook p39)
                                if (prtad) lbPRTE <= 1; else mbuf <= breakdata;
                            end
                            MS_DEPOS: begin
                                if (prtad) lbPRTE <= 1; else mbuf <= swSR;
                            end
                        endcase
                        timedelay <= 0;
                        timestate <= TS_TP2BEG;
                    end
                end

                TS_TP2BEG: begin
                    if (timedelay != 2) timedelay <= timedelay + 1;
                    else timestate <= TS_TP2END;
                end

                TS_TP2END: begin
                    if (timedelay != 5) timedelay <= timedelay + 1;
                    else begin timedelay <= 0; timestate <= TS_TS3BODY; end
                end

                ////////////////////////////////////////
                //  write MB back to memory location  //
                ////////////////////////////////////////

                // write modification or original data in MB back to memory
                // - this state lasts for 280nS
                TS_TS3BODY: begin

                    // like a real PDP, compute next major state in time for TP3
                    // mostly needed by pdp8lxmem.v
                    if (timedelay == 0) begin
                        if (lbPRTE) nextmajst <= MS_HALT;
                        else case (majstate)

                            // nearing end of FETCH cycle
                            MS_FETCH: begin
                                case (ireg)

                                    // add, tad, isz, dca, jms
                                    0, 1, 2, 3, 4: nextmajst <= mbuf[08] ? MS_DEFER : MS_EXEC;

                                    // jmp
                                    5: nextmajst <= mbuf[08] ? MS_DEFER : hltbrkintfet;

                                    // iot, opr
                                    6, 7: nextmajst <= hltbrkintfet;
                                endcase
                            end

                            // nearing end of DEFER cycle
                            MS_DEFER: nextmajst <= (ireg == 5) ? hltbrkintfet : MS_EXEC;

                            // nearing end of EXEC cycle
                            MS_EXEC, MS_INTAK: nextmajst <= hltbrkintfet;

                            // nearing end of wordcount
                            MS_WC: nextmajst <= MS_CA;

                            // nearing end of currentaddress
                            MS_CA: nextmajst <= MS_BRK;

                            // nearing end of break-while-running
                            MS_BRK: nextmajst <= hltbrkintfet;

                            // something else, halt next
                            default: nextmajst <= MS_HALT;
                        endcase
                    end

                    // wait 230nS, clock into memory then start TP3
                    // if external memory, pdp8lxmem.v clocked data in somewhere in middle of TS3
                    if (timedelay != 23) timedelay <= timedelay + 1;
                    else begin
                        if (memen) begin
                            localcore[madr] <= mbuf;
                        end
                        timedelay <= 0;
                        timestate <= TS_TP3BEG;
                    end
                end

                TS_TP3BEG: begin
                    o_BWC_OVERFLOW <= 1;    // PDP-8/L clears BWC_OVERFLOW at end of TS3 (vol 2, p9 D-5)
                    if (timedelay != 2) timedelay <= timedelay + 1;
                    else timestate <= TS_TP3END;
                end

                TS_TP3END: begin
                    if (timedelay != 5) timedelay <= timedelay + 1;
                    else begin
                        timedelay <= 0;
                        timestate <= withio ? TS_BEGIOP1 : TS_TS4BODY;
                    end
                end

                //////////////////////////////////////////////////
                //  if io instruction, output the three pulses  //
                //////////////////////////////////////////////////

                // delay between end of memory cycle and start of first io pulse
                TS_BEGIOP1: begin
                    if (timedelay != 28) timedelay <= timedelay + 1;
                    else begin timedelay <= 0; timestate <= TS_DOIOP1; end
                end

                // output first io pulse for 580nS
                TS_DOIOP1: begin
                    if (timedelay != 58) timedelay <= timedelay + 1;
                    else begin
                        if (mbuf[08:00] == 1) begin  // 06001 = ION
                            intdelayed <= 1;
                        end
                        acum <= ioac;
                        if (iIO_SKIP) pctr <= pctr + 1;
                        timedelay <= 0;
                        timestate <= TS_BEGIOP2;
                    end
                end

                // delay 300nS between first and second io pulse
                // real PDP-8/L is 280nS, but stretch for 4.25uS IO instr time
                TS_BEGIOP2: begin
                    if (timedelay != 30) timedelay <= timedelay + 1;
                    else begin timedelay <= 0; timestate <= TS_DOIOP2; end
                end

                // output second io pulse for 580nS
                TS_DOIOP2: begin
                    if (timedelay != 58) timedelay <= timedelay + 1;
                    else begin
                        if (mbuf[08:00] == 2) begin  // 06002 = IOF
                            intdelayed <= 0;
                            intenabled <= 0;
                        end
                        acum <= ioac;
                        if (iIO_SKIP) pctr <= pctr + 1;
                        timedelay <= 0;
                        timestate <= TS_BEGIOP4;
                    end
                end

                // delay 300nS between second and third io pulse
                // real PDP-8/L is 280nS, but stretch for 4.25uS IO instr time
                TS_BEGIOP4: begin
                    if (timedelay != 30) timedelay <= timedelay + 1;
                    else begin timedelay <= 0; timestate <= TS_DOIOP4; end
                end

                // output third io pulse for 500nS
                TS_DOIOP4: begin
                    if (timedelay != 50) timedelay <= timedelay + 1;
                    else begin
                        acum <= ioac;
                        if (iIO_SKIP) pctr <= pctr + 1;
                        timedelay <= 0;
                        timestate <= TS_TS4BODY;
                    end
                end

                ///////////////////////////////
                //  finish the memory cycle  //
                ///////////////////////////////
                // - do any final processing for the state such as update acum, link, pctr

                // finish up this cycle (340nS)
                TS_TS4BODY: begin
                    if (timedelay == 0) newma <= madr;
                    if (timedelay == 1) begin

                        // real PDP-8/L updates AC via TP3 so update it here at beginning of TS4
                        // also compute new MA to be loaded at TP4 like real PDP-8/L

                        // finish off cycle
                        case (majstate)

                            // end of FETCH cycle
                            MS_FETCH: begin
                                case (ireg)

                                    // add, tad, isz, dca, jms
                                    0, 1, 2, 3, 4: newma <= effaddr;

                                    // jmp
                                    5: begin
                                        if (mbuf[08]) newma <= effaddr;
                                                 else pctr <= effaddr;
                                    end

                                    // opr - perform operation and start another fetch
                                    7: begin
                                        if (~ mbuf[08]) begin
                                            acum <= g1acum;
                                            link <= g1link;
                                        end else if (~ mbuf[00]) begin
                                            acum <= g2acum;
                                            if (g2skip) pctr <= pctr + 1;
                                        end
                                    end
                                endcase
                            end

                            // end of DEFER cycle
                            MS_DEFER: begin
                                if (ireg == 5) pctr <= mbuf;
                                          else newma <= mbuf;
                            end

                            // end of EXEC cycle
                            MS_EXEC, MS_INTAK: begin
                                case (ireg)
                                    0: acum <= acum & mbuf;                         // and
                                    1: begin link <= tadlink; acum <= tadacum; end  // tad
                                    2: if (mbuf == 0) pctr <= pctr + 1;             // isz
                                    3: acum <= 0;                                   // dca
                                    4: pctr <= madr + 1;                            // jms
                                endcase
                            end

                            // end of wordcount
                            MS_WC: newma <= madr + 1;
                        endcase
                    end

                    if (timedelay != 34) begin
                        timedelay <= timedelay + 1;
                    end else begin
                        timedelay <= 0;
                        timestate <= TS_TP4BEG;
                    end
                end

                TS_TP4BEG: begin
                    case (timedelay)
                        0: begin
                            if (majstate == MS_BRK) begin
                                o_ADDR_ACCEPT <= 0;         // 350-450nS pulse starting at TP4 (pdp-8/l users handbook p38)
                                                            // ends with next cycle STROBE pulse (TP1)
                            end
                            case (nextmajst)
                                MS_FETCH: madr <= pctr;
                                MS_WC:    madr <= iDMAADDR;
                                MS_BRK:   madr <= (majstate == MS_CA) ? mbuf : iDMAADDR;
                                MS_INTAK: begin
                                    intdelayed <= 0;
                                    intenabled <= 0;
                                    ireg       <= 4;
                                    madr       <= 0;
                                end
                                default: madr <= newma;
                            endcase
                            timedelay <= 1;
                        end
                        1: if (memen | memidle) begin
                            timedelay <= 2;
                        end
                        2: begin
                            majstate  <= nextmajst;
                            timestate <= TS_TP4END;
                        end
                    endcase
                end

                TS_TP4END: begin
                    if (timedelay != 5) timedelay <= timedelay + 1;
                    else timestate <= TS_TSIDLE;
                end
            endcase

            // debounce front-panel momentary switches
            if (~ (swCONT | swDEP | swEXAM | swLDAD | swSTART)) debounce <= 0;
            else if (~ debounced) debounce <= debounce + 1;

            // save these for transition testing
            lastswCONT  <= swCONT;
            lastswDEP   <= swDEP;
            lastswEXAM  <= swEXAM;
            lastswLDAD  <= swLDAD;
            lastswSTART <= swSTART;

            // keep track of external memory state
            // it is only valid for external memory cuz i_STROBE,i_MEMDONE are only for external memory
            // see vol 2 p4 C-8
            if (~ i_STROBE) memidle <= 0;           // waiting for i_MEMDONE for this cycle
            else if (~ i_MEMDONE) memidle <= 1;     // got i_MEMDONE for this cycle
        end
    end
endmodule
