mrieker/pdp8l/zynq/pdp8lpbit.v

//    Copyright (C) Mike Rieker, Beverly, MA USA
//    www.outerworldapps.com
//
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
//    EXPECT it to FAIL when someone's HeALTh or PROpeRTy is at RISk.
//
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
//    http://www.gnu.org/licenses/gpl-2.0.html

// PDP-8/L pulse bit generator

// arm registers:
//  [0] = ident='PB',sizecode=0,version
//  [1] = iszac 00000 width count

module pdp8lpbit (
    input CLOCK, CSTEP, RESET,

    input armwrite,
    input[2:0] armraddr, armwaddr,
    input[31:00] armwdata,
    output[31:00] armrdata,

    input iopstart,
    input iopstop,
    input[11:00] ioopcode,
    input[11:00] cputodev,

    output reg[11:00] devtocpu,
    output reg AC_CLEAR,
    output reg IO_SKIP,

    output reg pulse
);

    reg iszac, lastpulse;
    reg [12:00] count, width;
    reg [15:00] samprate, sampincr, sampcount, sampinteg;
    reg [31:00] sampbytes;
    reg [15:00] fcount, ffinal;
    reg [26:00] onesec;

    assign armrdata = (armraddr == 0) ? 32'h50422006 : // [31:16] = 'PB'; [15:12] = (log2 nreg) - 1; [11:00] = version
                      (armraddr == 1) ? { iszac, 5'b0, width, count } :
                      (armraddr == 2) ? { samprate, sampincr } :
                      (armraddr == 3) ? sampbytes :
                      (armraddr == 4) ? { 5'b0, onesec } :
                      (armraddr == 5) ? { ffinal, fcount } :
                                        32'hDEADBEEF;

    always @(posedge CLOCK) begin
        if (RESET) begin
            iszac  <= 0;        // don't do ISZ AC
            width  <= 599;      // 6.00uS pulse width
            count  <= 0;
            pulse  <= 0;
            onesec <= 0;
            fcount <= 0;
            ffinal <= 0;
            lastpulse <= 0;
        end else begin

            // arm processor is writing the register
            if (armwrite) begin
                case (armwaddr)
                    1: begin
                        iszac <= armwdata[31];
                        width <= armwdata[25:13];
                        count <= 0;
                        pulse <= 0;
                    end
                    2: begin
                        samprate  <= armwdata[31:16];
                        sampincr  <= armwdata[15:00];
                        sampcount <= 0;
                        sampinteg <= 0;
                        sampbytes <= 0;
                    end
                endcase
            end else if (CSTEP) begin
                if (iopstart) begin

                    // any I/O instruction, start pulse going
                    count <= width;
                    pulse <= 1;

                    // maybe do increment accumulator and skip if zero
                    if (iszac & (ioopcode == 12'o6004)) begin
                        AC_CLEAR <= 1;
                        { IO_SKIP, devtocpu } <= { 1'b0, cputodev } + 13'o00001;
                    end
                end else begin
                    if (iopstop) begin
                        devtocpu <= 0;
                        AC_CLEAR <= 0;
                        IO_SKIP  <= 0;
                    end
                    if (count != 0) begin
                        count <= count - 1;
                    end else begin
                        pulse <= 0;
                    end
                end

                // at 8000 samples/second:
                //  samprate = 100000000 / 8000 - 1 = 12499
                //  sampincr = 65535 / (samprate + 1) = 5
                if (sampcount == samprate) begin
                    sampbytes <= { sampbytes[23:00], sampinteg[15:08] };
                    sampcount <= 0;
                    sampinteg <= pulse ? sampincr : 0;
                end else begin
                    sampcount <= sampcount + 1;
                    if (pulse) sampinteg <= sampinteg + sampincr;
                end
            end

            // run a frequency counter
            // counts the 0-to-1 transitions of pulse
            if (onesec == 99999999) begin
                onesec <= 0;
                ffinal <= fcount;
                fcount <= { 15'b0, ~ lastpulse & pulse };
            end else begin
                onesec <= onesec + 1;
                if (~ lastpulse & pulse & (fcount != 65535)) begin
                    fcount <= fcount + 1;
                end
            end

            lastpulse <= pulse;
        end
    end
endmodule
