mrieker/pdp8l/pipan8l/z8lvc8.cc

//    Copyright (C) Mike Rieker, Beverly, MA USA
//    www.outerworldapps.com
//
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
//    EXPECT it to FAIL when someone's HeALTh or PROpeRTy is at RISk.
//
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
//    http://www.gnu.org/licenses/gpl-2.0.html

// VC8 small computer handbook PDP-8/I, 1970, p87

#include <fcntl.h>
#include <string.h>
#include <sys/time.h>
#include <unistd.h>
#include <X11/Xlib.h>

#include "z8ldefs.h"
#include "z8lutil.h"

#define MAXBUFFPTS 32768    // size of pdp8lvc8.v videoram
#define DEFPERSISTMS 500    // how long non-storage points last
#define MINPERSISTMS 10     // ...smaller and the up/down buttons won't work
#define MAXPERSISTMS 60000  // ...larger and it will overflow 16-bit counter

#define XYSIZE 1024
#define DEFWINSIZE XYSIZE
#define MINWINSIZE 64
#define MAXWINSIZE XYSIZE
#define BORDERWIDTH 2

#define EF_DN 04000     // done executing last command
#define EF_WT 00040     // de-focus beam for writing
#define EF_ST 00020     // enable storage mode
#define EF_ER 00010     // erase storage screen (450ms)
#define EF_CO 00004     // 1=red; 0=green
#define EF_CH 00002     // display select
#define EF_IE 00001     // interrupt enable

#define EF_MASK 077

enum VC8Type {
    VC8TypeN = 0,
    VC8TypeE = 1,
    VC8TypeI = 2
};

struct VC8Pt {
    uint16_t x;
    uint16_t y;
    uint16_t t;
};

struct Button {
    Button ();
    virtual ~Button ();

    virtual void draw (unsigned long color) = 0;
    bool clicked ();

protected:
    bool lastpressed;
    int xleft, xrite, ytop, ybot;
};

struct ClearButton : Button {
    ClearButton ();
    void position ();
    virtual void draw (unsigned long color);
};

struct TriButton : Button {
    TriButton (bool upbut);
    void position ();
    virtual void draw (unsigned long color);

private:
    bool upbut;
    XSegment segs[3];
};

struct PersisButton {
    TriButton upbutton;
    TriButton dnbutton;

    PersisButton ();
    void setpms ();
    void draw (unsigned long color);

private:
    char pmsbuf[12];
    int pmslen;
};

static bool mintimes;
static int winsize;
static unsigned long xwin;
static _XDisplay *xdis;
static _XGC *xgc;
static int indices[MAXWINSIZE*MAXWINSIZE];
static uint16_t pms;
static uint16_t timemss[XYSIZE*XYSIZE];
static unsigned long blackpixel;
static unsigned long foreground;
static unsigned long graylevels[6];
static unsigned long whitepixel;
static VC8Pt allpoints[XYSIZE*XYSIZE];
static VC8Type vc8type;

static void thread ();
static void drawpt (int i, bool erase);
static int mappedxy (VC8Pt const *pt);
static void setfg (unsigned long color);
static int xioerror (Display *xdis);
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
